mobilinkd/NucleoTNC/m17/images/m17-audio-output.png

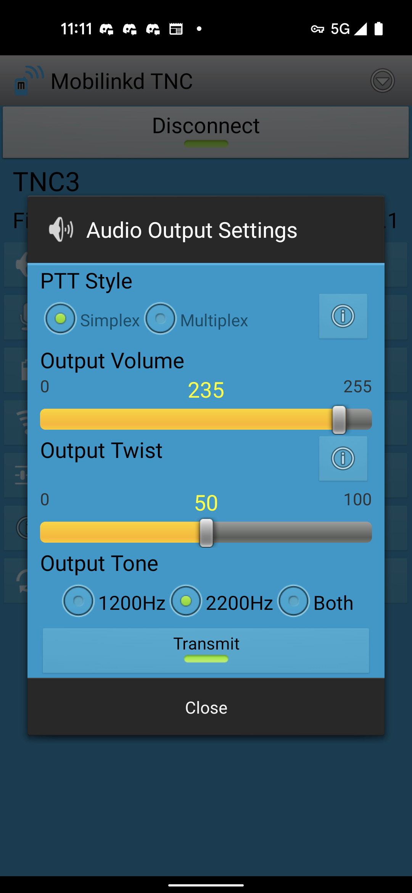
m17/images/m17-audio-output.png
