mobilinkd/NucleoTNC/m17/images/m17-bessel-null.png

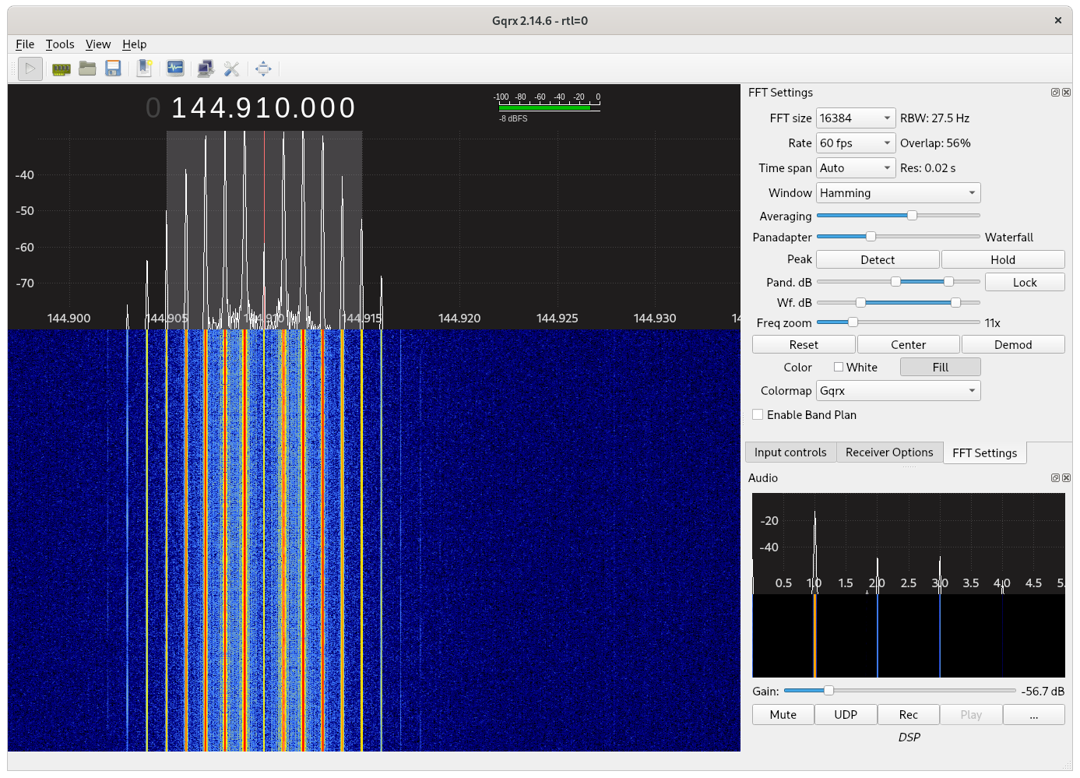
m17/images/m17-bessel-null.png
