mobilinkd/NucleoTNC/m17/images/m17-ht-voice-transmit.png

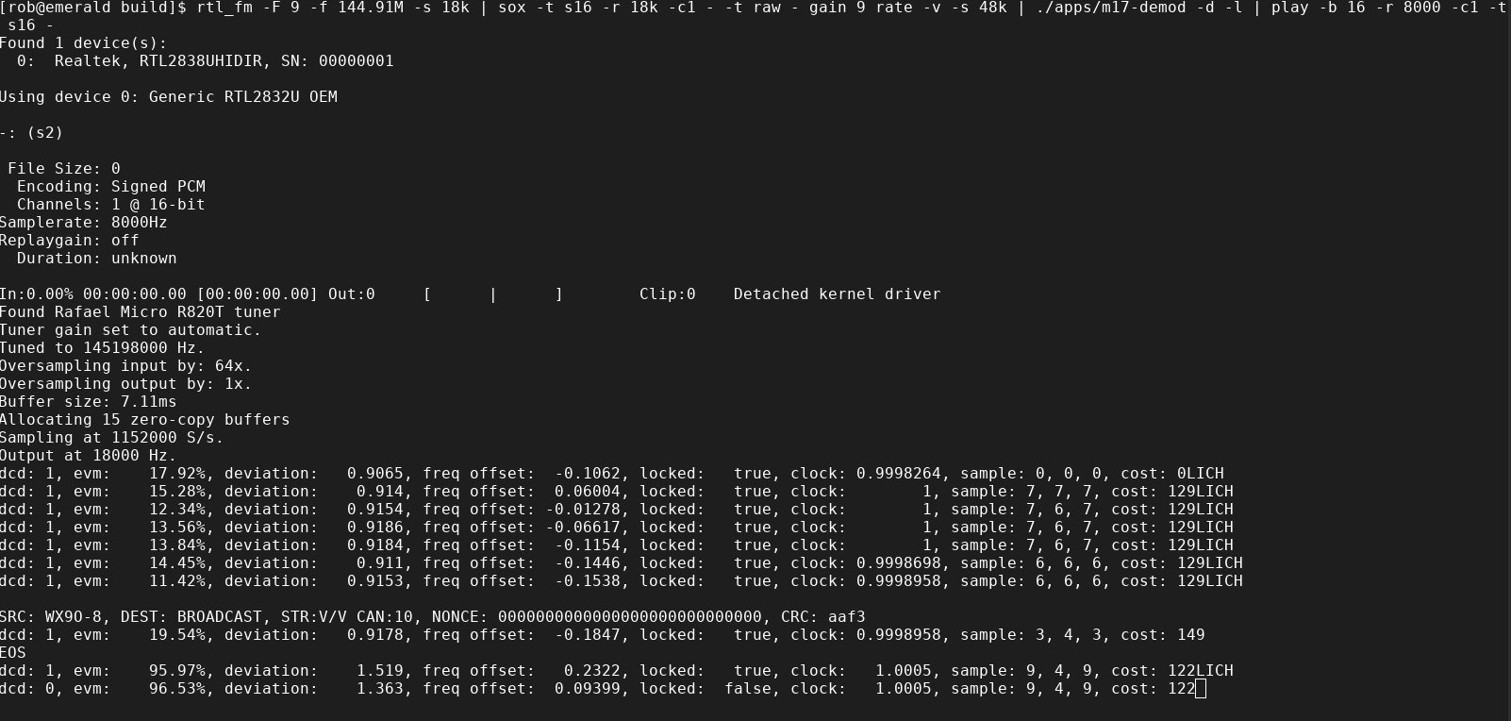
m17/images/m17-ht-voice-transmit.png
