mobilinkd/NucleoTNC/m17/images/m17-kiss-ht-callsign.png

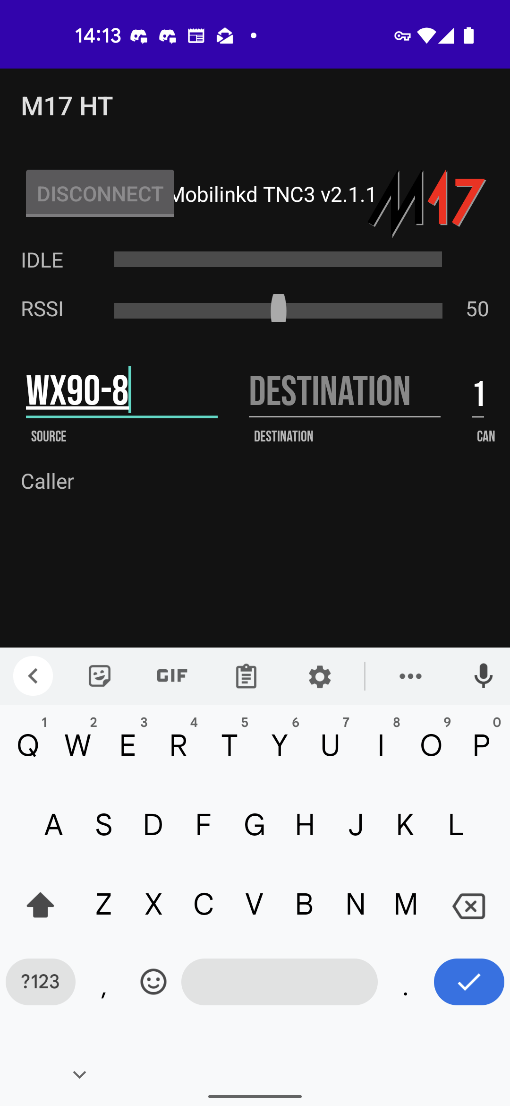
m17/images/m17-kiss-ht-callsign.png
