mobilinkd/NucleoTNC/m17/images/m17-modem-settings.png

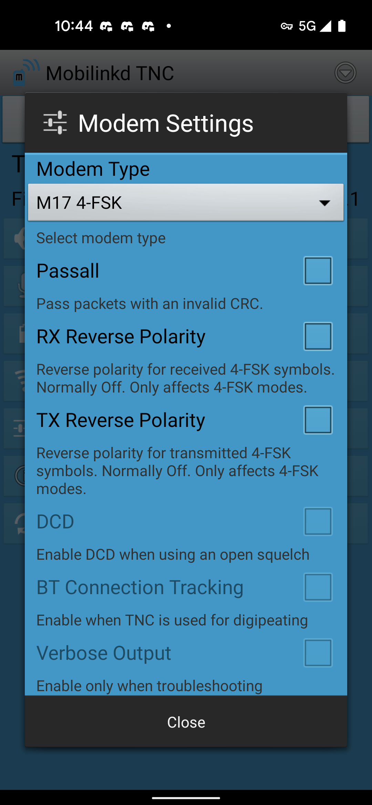
m17/images/m17-modem-settings.png
