mobilinkd/NucleoTNC/m17/images/m17-usb-connection.png

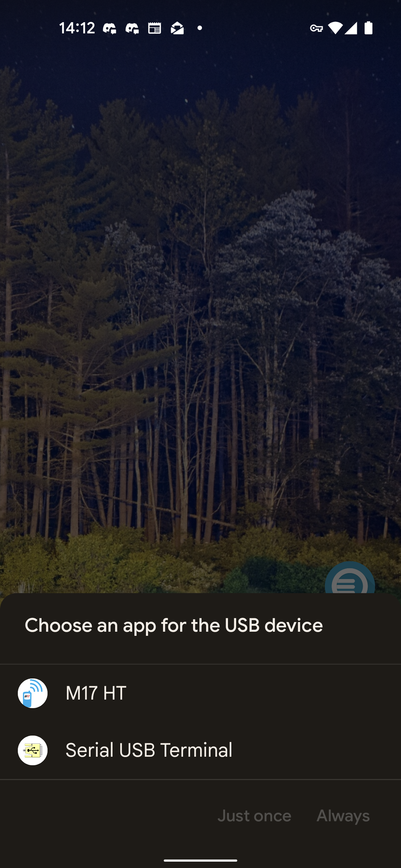
m17/images/m17-usb-connection.png
