mobilinkd/NucleoTNC/m17/images/wobbly-freq-accuracy.png

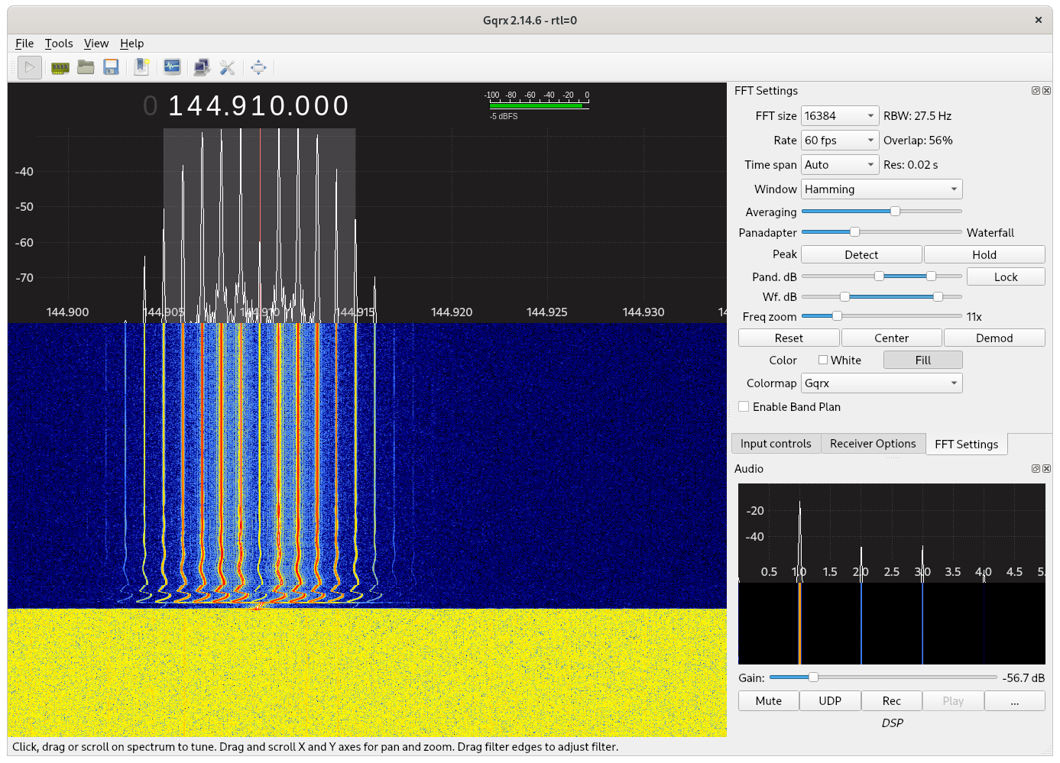
m17/images/wobbly-freq-accuracy.png
