mobilinkd/NucleoTNC/Build/AssemblyStep1.png

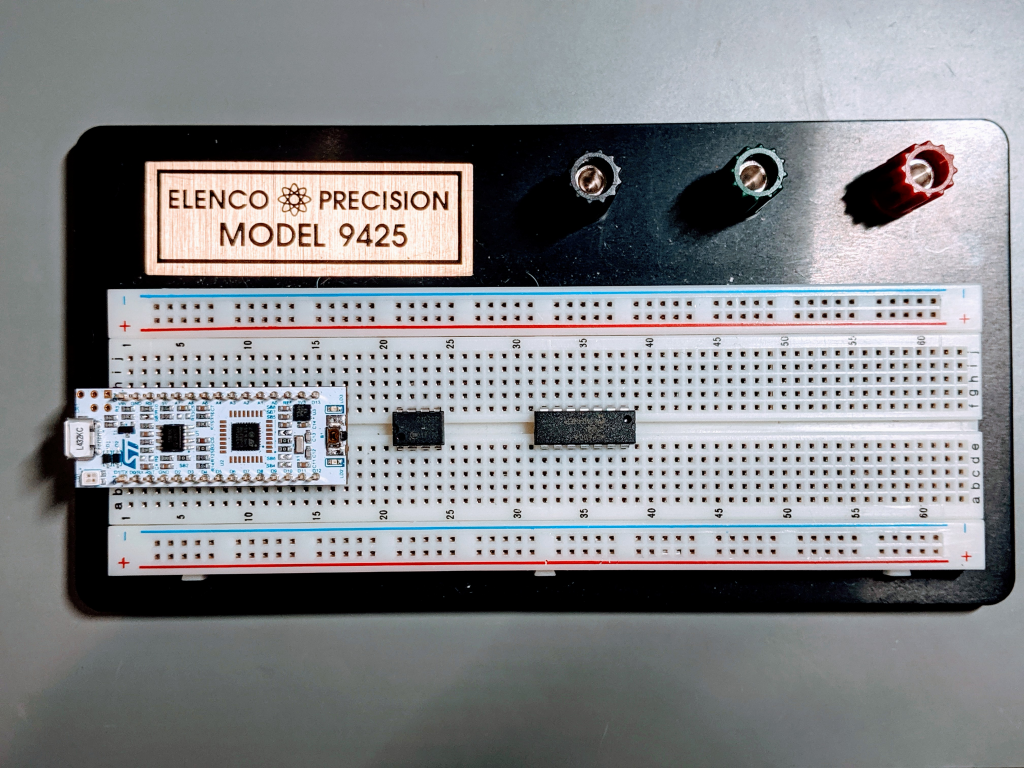
Build/AssemblyStep1.png
