mobilinkd/NucleoTNC/Build/AssemblyStep2.png

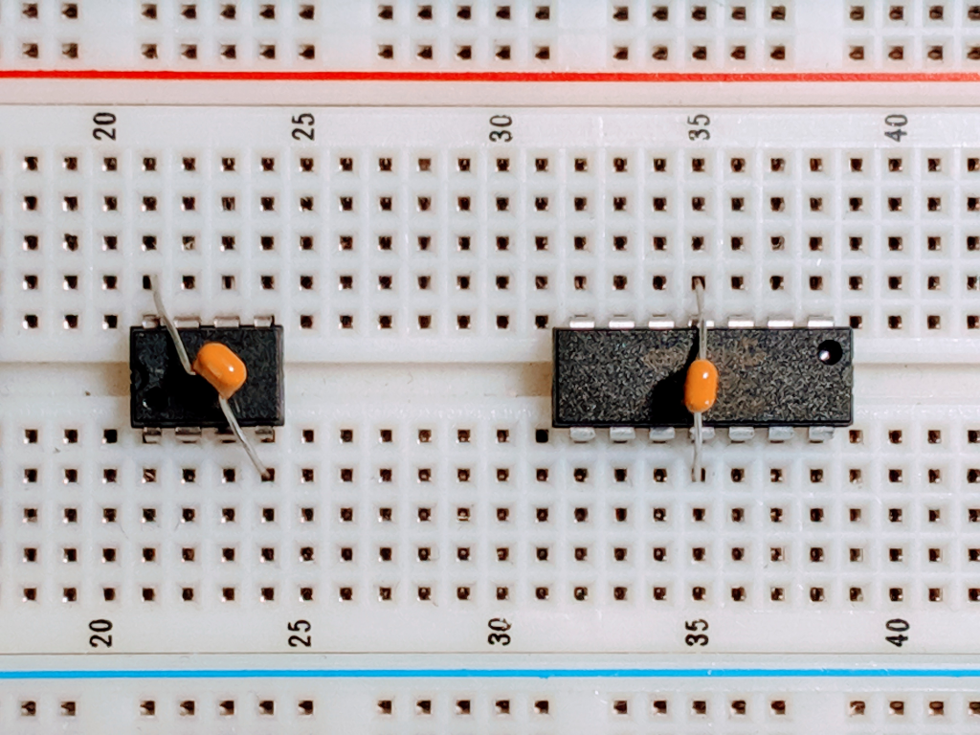
Build/AssemblyStep2.png
