mobilinkd/NucleoTNC/Build/AssemblyStep5.png

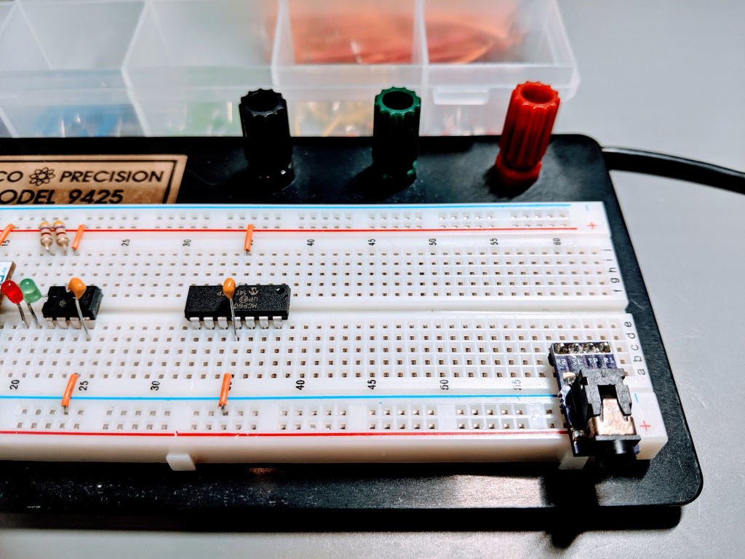
Build/AssemblyStep5.png
