mobilinkd/NucleoTNC/Build/AssemblyStep6.png

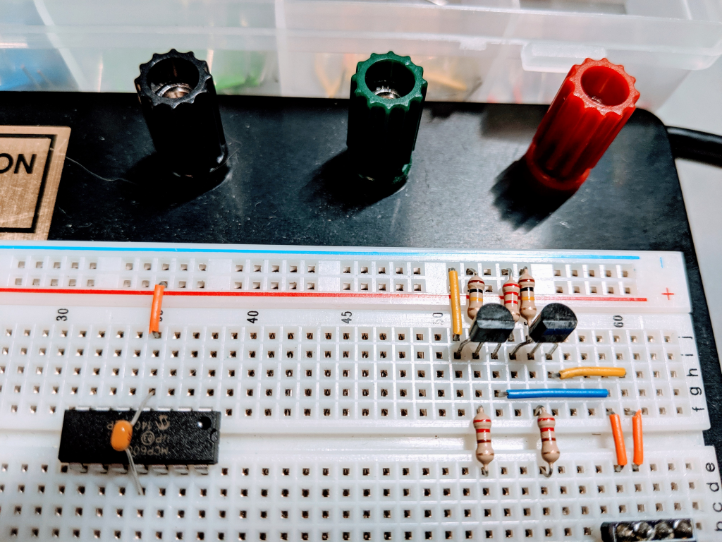
Build/AssemblyStep6.png
