mobilinkd/NucleoTNC/Build/AssemblyStep7.png

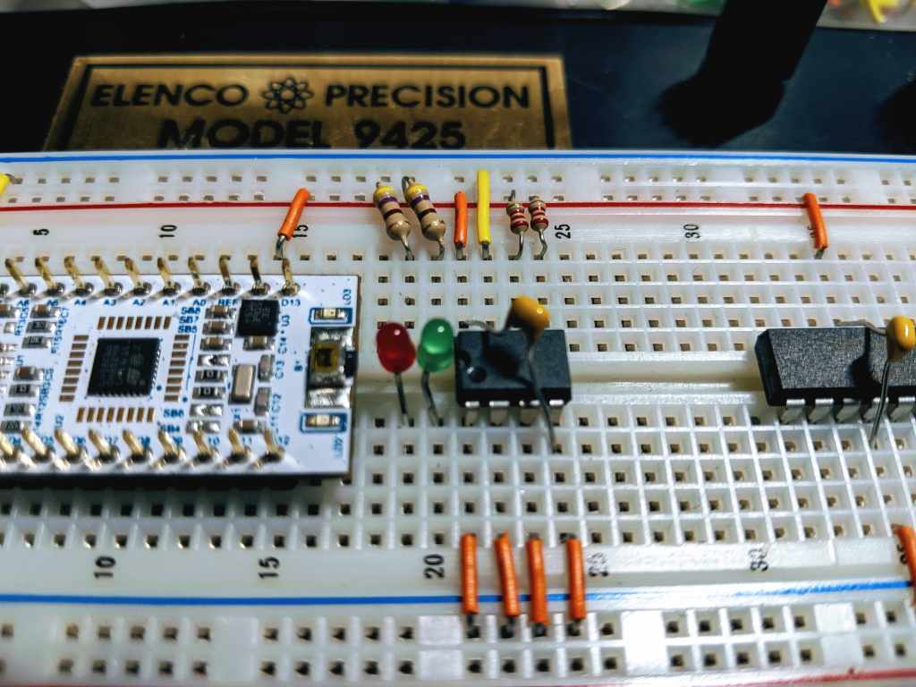
Build/AssemblyStep7.png
