mobilinkd/NucleoTNC/Build/AssemblyStep8.png

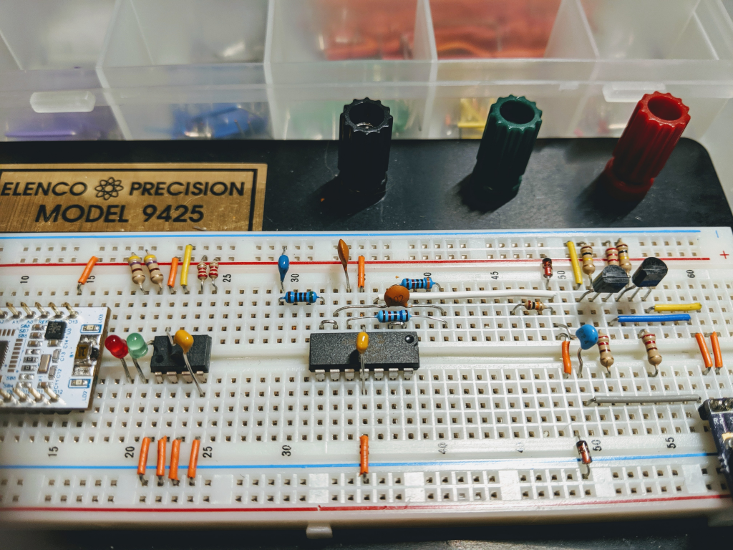
Build/AssemblyStep8.png
