mobilinkd/NucleoTNC/Build/AssemblyStep9.png

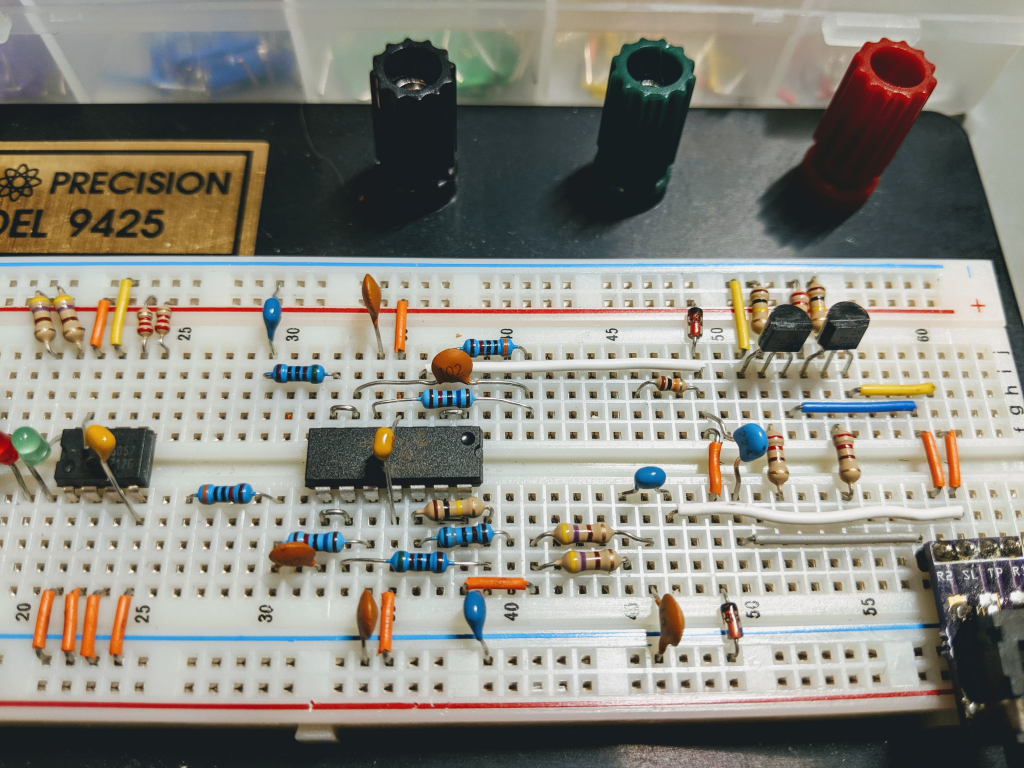
Build/AssemblyStep9.png
