mobilinkd/NucleoTNC/Build/TncConfigApp-Connect.png

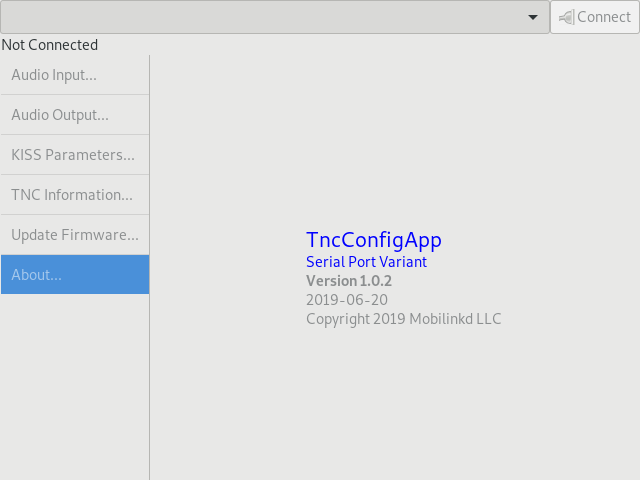
Build/TncConfigApp-Connect.png
