mobilinkd/NucleoTNC/Build/TncConfigApp-Info.png

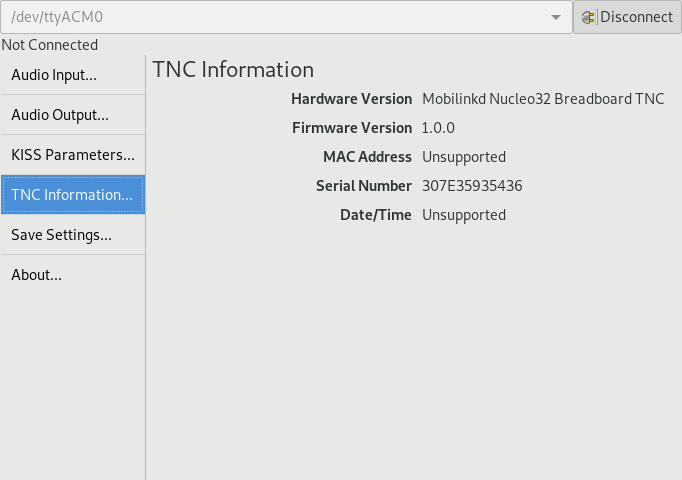
Build/TncConfigApp-Info.png
