mobilinkd/NucleoTNC/Build/TncConfigApp-Output.png

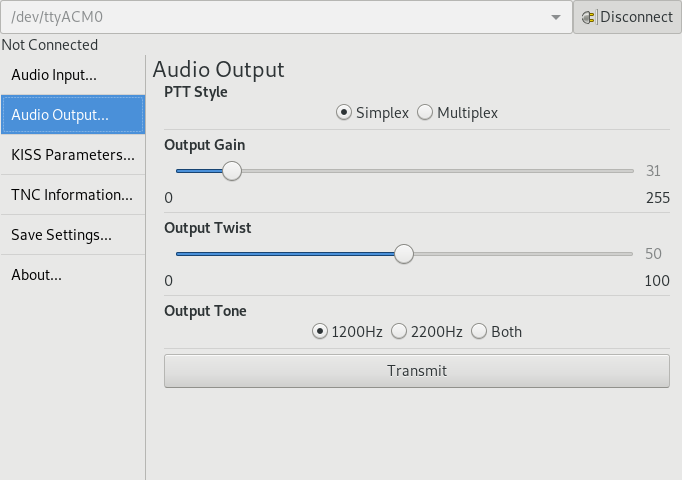
Build/TncConfigApp-Output.png
