mobilinkd/NucleoTNC/m17/images/m17-ber-test-1.png

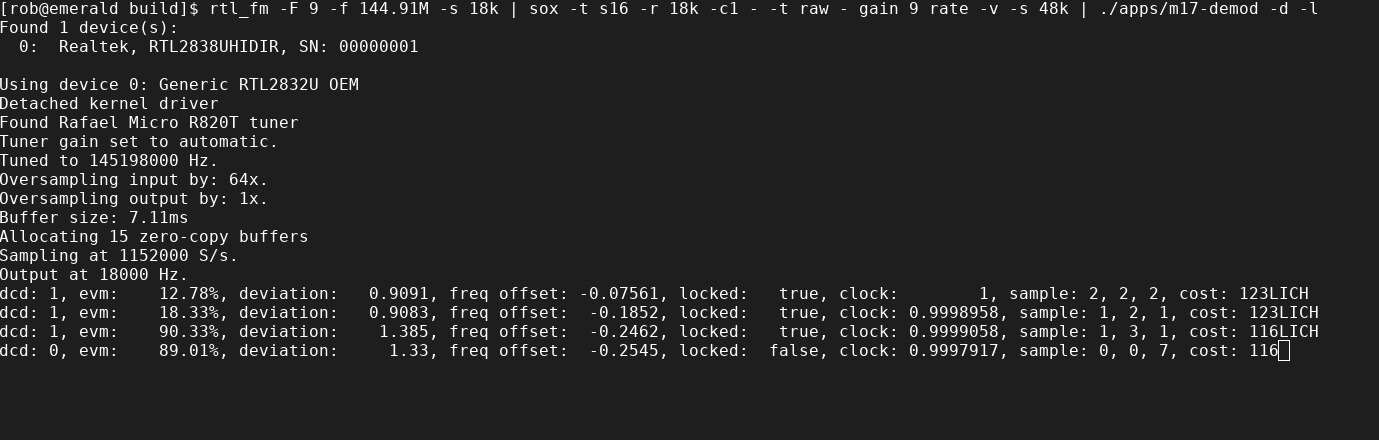
m17/images/m17-ber-test-1.png
