mobilinkd/NucleoTNC/m17/images/m17-ber-test-2.png

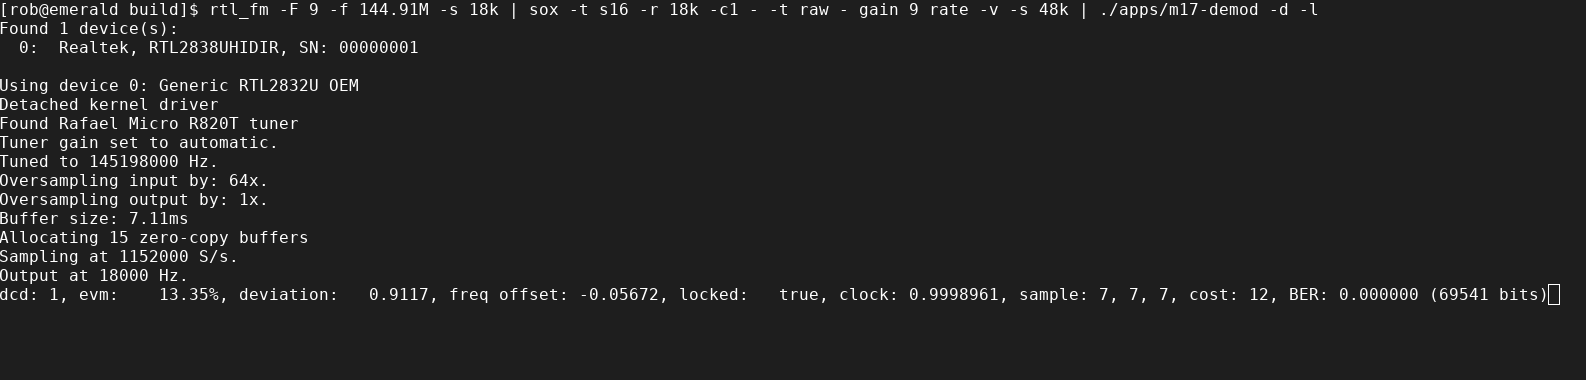
m17/images/m17-ber-test-2.png
