mobilinkd/NucleoTNC/m17/images/m17-rx-ber-test.png

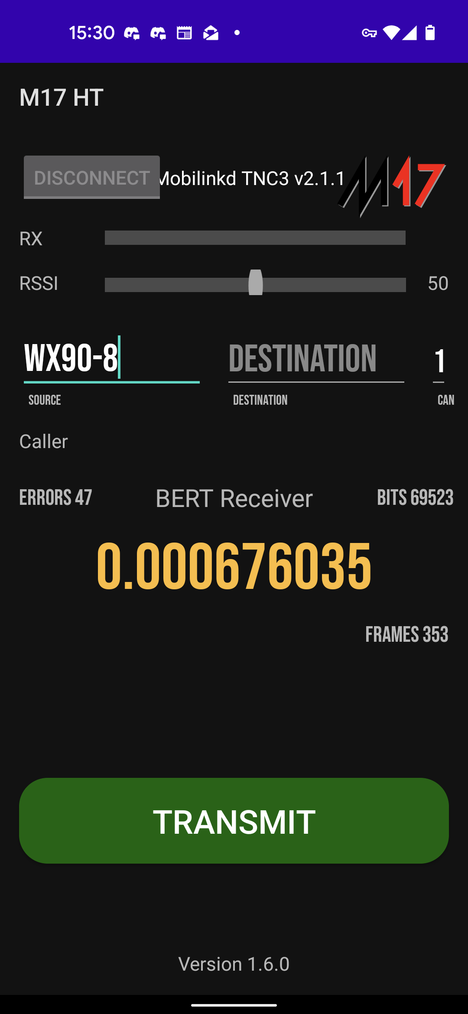
m17/images/m17-rx-ber-test.png
