mobilinkd/NucleoTNC/m17/images/m17-rx-voice-test.png

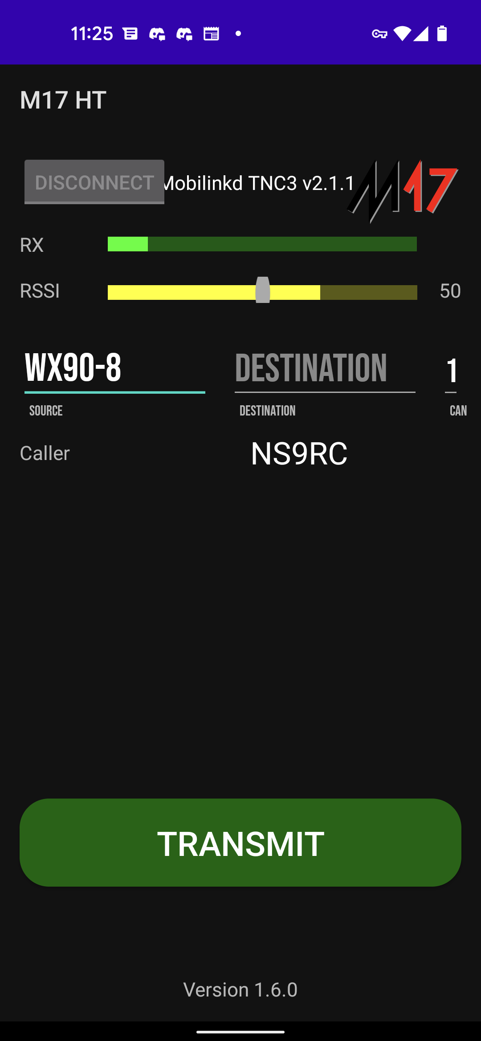
m17/images/m17-rx-voice-test.png
