mobilinkd/NucleoTNC/TNC/Fsk9600Demodulator.cpp

// Copyright 2020 Rob Riggs <rob@mobilinkd.com>
// All rights reserved.

#include "Fsk9600Demodulator.hpp"
#include "Goertzel.h"
#include "AudioInput.hpp"
#include "GPIO.hpp"
#include "Log.h"

namespace mobilinkd { namespace tnc {

hdlc::IoFrame* Fsk9600Demodulator::operator()(const q15_t* samples)
{
    hdlc::IoFrame* result = nullptr;

    auto filtered = demod_filter.filter(const_cast<q15_t* >(samples));

    for (size_t i = 0; i != ADC_BLOCK_SIZE; ++i)
    {
        auto sample = filtered[i];

        bool bit = sample >= 0;
        auto pll = pll_(bit);

        if (pll.sample)
        {
            locked_ = pll.locked;

            // We will only ever get one frame because there are
            // not enough bits in a block for more than one.
            if (result) {
                auto tmp = hdlc_decoder_(nrzi_.decode(lfsr_(bit)), locked_);
                if (tmp) hdlc::release(tmp);
            } else {
                result = hdlc_decoder_(nrzi_.decode(lfsr_(bit)), locked_);
#ifdef KISS_LOGGING
                if (result) {
                    INFO("samples = %ld, mean = %d, dev = %d",
                        snr_.samples, int(snr_.mean), int(snr_.stdev()));
                    INFO("SNR = %dmB", int(snr_.SNR() * 100.0f));
                    snr_.reset();
                }
#endif
            }

#ifdef KISS_LOGGING
            if (hdlc_decoder_.active())
            {
                if (!decoding_)
                {
                    snr_.reset();
                    decoding_ = true;
                }
                snr_.capture(float(abs(sample)));
            } else {
                decoding_ = false;
            }
#endif
        }

    }
    return result;
}

/*
 * Return twist as a the difference in dB between mark and space.  The
 * expected values are about 0dB for discriminator output and about 5.5dB
 * for de-emphasized audio.
 */
float Fsk9600Demodulator::readTwist()
{
    TNC_DEBUG("enter Fsk9600Demodulator::readTwist");

    float g120 = 0.0f;
    float g4800 = 0.0f;

    GoertzelFilter<ADC_BLOCK_SIZE, SAMPLE_RATE> gf120(120.0, 0);
    GoertzelFilter<ADC_BLOCK_SIZE, SAMPLE_RATE> gf4800(4800.0, 0);

    const uint32_t AVG_SAMPLES = 160;

    startADC(416, ADC_BLOCK_SIZE);

    for (uint32_t i = 0; i != AVG_SAMPLES; ++i)
    {
        uint32_t count = 0;
        while (count < ADC_BLOCK_SIZE)
        {
            osEvent evt = osMessageGet(adcInputQueueHandle, osWaitForever);
            if (evt.status != osEventMessage)
                continue;

            auto block = (audio::adc_pool_type::chunk_type*) evt.value.p;
            uint16_t* data = (uint16_t*) block->buffer;
            gf120(data, ADC_BLOCK_SIZE);
            gf4800(data, ADC_BLOCK_SIZE);

            audio::adcPool.deallocate(block);

            count += ADC_BLOCK_SIZE;
        }

        g120 += (gf120 / count);
        g4800 += (gf4800 / count);

        gf120.reset();
        gf4800.reset();
    }

    IDemodulator::stopADC();

    g120 = 10.0f * log10f(g120 / AVG_SAMPLES);
    g4800 = 10.0f * log10f(g4800 / AVG_SAMPLES);

    auto result = g120 - g4800;

    INFO("9600 Twist = %d / 100 (%d - %d)", int(result * 100), int(g120 * 100),
        int(g4800 * 100));

    TNC_DEBUG("exit Fsk9600Demodulator::readTwist");
    return result;
}

uint32_t Fsk9600Demodulator::readBatteryLevel()
{
#ifndef NUCLEOTNC
    TNC_DEBUG("enter Fsk9600Demodulator::readBatteryLevel");

    ADC_ChannelConfTypeDef sConfig;

    sConfig.Channel = ADC_CHANNEL_VREFINT;
    sConfig.Rank = ADC_REGULAR_RANK_1;
    sConfig.SingleDiff = ADC_SINGLE_ENDED;
    sConfig.SamplingTime = ADC_SAMPLETIME_247CYCLES_5;
    sConfig.OffsetNumber = ADC_OFFSET_NONE;
    sConfig.Offset = 0;
    if (HAL_ADC_ConfigChannel(&hadc1, &sConfig) != HAL_OK)
        CxxErrorHandler();

    htim6.Init.Period = 48000;
    if (HAL_TIM_Base_Init(&htim6) != HAL_OK) CxxErrorHandler();

    if (HAL_TIM_Base_Start(&htim6) != HAL_OK)
        CxxErrorHandler();

    if (HAL_ADC_Start(&hadc1) != HAL_OK) CxxErrorHandler();
    if (HAL_ADC_PollForConversion(&hadc1, 3) != HAL_OK) CxxErrorHandler();
    auto vrefint = HAL_ADC_GetValue(&hadc1);
    if (HAL_ADC_Stop(&hadc1) != HAL_OK) CxxErrorHandler();

    // Disable battery charging while measuring battery voltage.
    auto usb_ce = gpio::USB_CE::get();
    gpio::USB_CE::on();

    gpio::BAT_DIVIDER::off();
    HAL_Delay(1);

    sConfig.Channel = BATTERY_ADC_CHANNEL;
    if (HAL_ADC_ConfigChannel(&BATTERY_ADC_HANDLE, &sConfig) != HAL_OK)
        CxxErrorHandler();

    uint32_t vbat = 0;
    if (HAL_ADC_Start(&BATTERY_ADC_HANDLE) != HAL_OK) CxxErrorHandler();
    for (size_t i = 0; i != 8; ++i)
    {
        if (HAL_ADC_PollForConversion(&BATTERY_ADC_HANDLE, 1) != HAL_OK) CxxErrorHandler();
        vbat += HAL_ADC_GetValue(&BATTERY_ADC_HANDLE);
    }

    vbat /= 8;

    if (HAL_ADC_Stop(&BATTERY_ADC_HANDLE) != HAL_OK) CxxErrorHandler();
    if (HAL_TIM_Base_Stop(&htim6) != HAL_OK)
        CxxErrorHandler();

    gpio::BAT_DIVIDER::on();

    // Restore battery charging state.
    if (!usb_ce) gpio::USB_CE::off();

    INFO("Vref = %lu", vrefint);
    INFO("Vbat = %lu (raw)", vbat);

    // Order of operations is important to avoid underflow.
    vbat *= 6600;
    vbat /= (VREF + 1);

    uint32_t vref = ((vrefint * 3300) + (VREF / 2)) / VREF;

    INFO("Vref = %lumV", vref)
    INFO("Vbat = %lumV", vbat);

    TNC_DEBUG("exit Fsk9600Demodulator::readBatteryLevel");
    return vbat;
#else
    return 0;
#endif
}

const Fsk9600Demodulator::bpf_bank_type Fsk9600Demodulator::bpf_bank = {{
    // -3dB
    {{
            1,     0,     0,     0,     0,     0,    -1,    -1,    -1,    -1,     0,     0,
            0,     0,     1,     2,     2,     3,     2,     2,     0,     0,    -2,    -3,
           -4,    -4,    -3,    -1,     3,     9,    17,    27,    38,    48,    58,    65,
           68,    67,    60,    46,    25,    -1,   -32,   -67,  -102,  -135,  -160,  -175,
         -174,  -153,  -110,   -41,    54,   178,   327,   500,   692,   897,  1109,  1318,
         1518,  1700,  1857,  1981,  2067,  2110,  2110,  2067,  1981,  1857,  1700,  1518,
         1318,  1109,   897,   692,   500,   327,   178,    54,   -41,  -110,  -153,  -174,
         -175,  -160,  -135,  -102,   -67,   -32,    -1,    25,    46,    60,    67,    68,
           65,    58,    48,    38,    27,    17,     9,     3,    -1,    -3,    -4,    -4,
           -3,    -2,     0,     0,     2,     2,     3,     2,     2,     1,     0,     0,
            0,     0,    -1,    -1,    -1,    -1,     0,     0,     0,     0,     0,     1
    }},
    // -2dB
    {{
            1,     0,     0,     0,     0,    -1,    -1,    -1,    -1,    -1,    -1,    -1,
            0,     0,     1,     1,     2,     2,     1,     0,     0,    -1,    -3,    -5,
           -6,    -6,    -5,    -1,     3,    10,    20,    31,    42,    54,    64,    72,
           75,    72,    63,    46,    21,   -11,   -49,   -92,  -135,  -175,  -208,  -229,
         -233,  -216,  -173,  -102,     0,   131,   293,   481,   691,   915,  1147,  1378,
         1598,  1799,  1971,  2108,  2203,  2251,  2251,  2203,  2108,  1971,  1799,  1598,
         1378,  1147,   915,   691,   481,   293,   131,     0,  -102,  -173,  -216,  -233,
         -229,  -208,  -175,  -135,   -92,   -49,   -11,    21,    46,    63,    72,    75,
           72,    64,    54,    42,    31,    20,    10,     3,    -1,    -5,    -6,    -6,
           -5,    -3,    -1,     0,     0,     1,     2,     2,     1,     1,     0,     0,
           -1,    -1,    -1,    -1,    -1,    -1,    -1,     0,     0,     0,     0,     1
    }},
    // -1dB
    {{
            1,     0,     0,     0,     0,    -1,    -1,    -2,    -2,    -2,    -2,    -1,
           -1,     0,     0,     0,     1,     1,     0,     0,    -1,    -3,    -5,    -7,
           -8,    -8,    -6,    -2,     3,    11,    22,    34,    48,    60,    72,    80,
           82,    78,    66,    45,    15,   -22,   -68,  -119,  -171,  -221,  -262,  -291,
         -300,  -286,  -244,  -170,   -62,    79,   255,   460,   689,   936,  1191,  1445,
         1688,  1909,  2100,  2251,  2356,  2410,  2410,  2356,  2251,  2100,  1909,  1688,
         1445,  1191,   936,   689,   460,   255,    79,   -62,  -170,  -244,  -286,  -300,
         -291,  -262,  -221,  -171,  -119,   -68,   -22,    15,    45,    66,    78,    82,
           80,    72,    60,    48,    34,    22,    11,     3,    -2,    -6,    -8,    -8,
           -7,    -5,    -3,    -1,     0,     0,     1,     1,     0,     0,     0,    -1,
           -1,    -2,    -2,    -2,    -2,    -1,    -1,     0,     0,     0,     0,     1
    }},
    // 0dB
    {{
            1,     0,     0,     0,    -1,    -1,    -2,    -2,    -3,    -3,    -3,    -2,
           -2,    -1,     0,     0,     0,     0,     0,    -1,    -3,    -5,    -7,    -9,
          -10,   -10,    -7,    -3,     3,    13,    25,    39,    53,    68,    80,    88,
           91,    85,    70,    45,     9,   -35,   -90,  -150,  -212,  -272,  -323,  -359,
         -376,  -366,  -324,  -247,  -132,    21,   212,   436,   688,   959,  1240,  1520,
         1789,  2034,  2244,  2412,  2528,  2587,  2587,  2528,  2412,  2244,  2034,  1789,
         1520,  1240,   959,   688,   436,   212,    21,  -132,  -247,  -324,  -366,  -376,
         -359,  -323,  -272,  -212,  -150,   -90,   -35,     9,    45,    70,    85,    91,
           88,    80,    68,    53,    39,    25,    13,     3,    -3,    -7,   -10,   -10,
           -9,    -7,    -5,    -3,    -1,     0,     0,     0,     0,     0,    -1,    -2,
           -2,    -3,    -3,    -3,    -2,    -2,    -1,    -1,     0,     0,     0,     1
    }},
    // 1dB
    {{
            1,     1,     0,     0,    -1,    -2,    -2,    -3,    -3,    -4,    -4,    -3,
           -3,    -2,    -1,    -1,    -1,    -1,    -1,    -3,    -5,    -7,    -9,   -11,
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
          -44,   -40,   -35,   -30,   -25,   -21,   -18,   -17,   -16,   -16,   -16,   -17,
          -17,   -16,   -15,   -14,   -12,    -9,    -7,    -4,    -2,     0,     2,     3
    }}
}};

}} // mobilinkd::tnc
