mobilinkd/NucleoTNC/TNC/Goertzel.cpp

// Copyright 2017 Rob Riggs <rob@mobilinkd.com>
// All rights reserved.

#include "Goertzel.h"

namespace mobilinkd { namespace tnc {

#if 1
const float WINDOW[] = {
  0.006878,
  0.00687800535762,
  0.00687802143048,
  0.00687804821858,
  0.00687808572193,
  0.00687813394055,
  0.00687819287442,
  0.00687826252358,
  0.00687834288804,
  0.00687843396781,
  0.00687853576292,
  0.00687864827338,
  0.00687877149922,
  0.00687890544047,
  0.00687905009716,
  0.00687920546932,
  0.00687937155698,
  0.00687954836018,
  0.00687973587896,
  0.00687993411336,
  0.00688014306342,
  0.0068803627292,
  0.00688059311073,
  0.00688083420806,
  0.00688108602126,
  0.00688134855038,
  0.00688162179547,
  0.00688190575659,
  0.00688220043381,
  0.00688250582719,
  0.0068828219368,
  0.0068831487627,
  0.00688348630498,
  0.0068838345637,
  0.00688419353893,
  0.00688456323077,
  0.00688494363928,
  0.00688533476456,
  0.00688573660669,
  0.00688614916575,
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

};

#endif

}} // mobilinkd::tnc
