mobilinkd/NucleoTNC/TNC/FilterCoefficients.hpp

// Copyright 2015-2020 Rob Riggs <rob@mobilinkd.com>
// All rights reserved.

#pragma once

#include "IirFilter.hpp"
#include "FirFilter.hpp"

namespace mobilinkd { namespace tnc { namespace filter {

namespace fir {

// 1200Hz = -12dB, 2200Hz = 0dB; 3653Hz cutoff, 4.93 gain; cosine.
const TFirCoefficients<9> dB12 = {
    {
        0.0223997567081,
        -0.132588208904,
        -0.590869965255,
        -1.12325491747,
        3.55525416434,
        -1.12325491747,
        -0.590869965255,
        -0.132588208904,
        0.0223997567081,
    }
};

// 1200Hz = -11dB, 2200Hz = 0dB; 3537Hz cutoff, 4.51 gain; cosine.
const TFirCoefficients<9> dB11 = {
    {
        0.0138943225784,
        -0.137800909104,
        -0.544488104185,
        -1.00269495093,
        3.29019584315,
        -1.00269495093,
        -0.544488104185,
        -0.137800909104,
        0.0138943225784,
    }
};

// 1200Hz = -10dB, 2200Hz = 0dB; 3405Hz cutoff, 4.11 gain; cosine.
const TFirCoefficients<9> dB10 = {
    {
        0.00564557245371,
        -0.141643920093,
        -0.498513944796,
        -0.887264289827,
        3.03792032485,
        -0.887264289827,
        -0.498513944796,
        -0.141643920093,
        0.00564557245371,
    }
};

// 1200Hz = -9dB, 2200Hz = 0dB; 3252Hz cutoff, 3.7 gain; cosine.
const TFirCoefficients<9> dB9 = {
    {
        -0.00232554104135,
        -0.142858725752,
        -0.449053780255,
        -0.770264863826,
        2.77651146344,
        -0.770264863826,
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
const TFirCoefficients<9> dB_4 = {
    {
        0.0498539382844,
        0.103801174967,
        0.153695746099,
        0.188874162863,
        0.201549955573,
        0.188874162863,
        0.153695746099,
        0.103801174967,
        0.0498539382844,
    }
};

// 1200Hz = 0dB, 2200Hz = -5dB; 2174Hz cutoff, 1.237 gain; boxcar.
const TFirCoefficients<9> dB_5 = {
    {
        0.0782137588209,
        0.118736939542,
        0.153156300897,
        0.176223458893,
        0.184339083696,
        0.176223458893,
        0.153156300897,
        0.118736939542,
        0.0782137588209,
    }
};

// 1200Hz = 0dB, 2200Hz = -6dB; 1706Hz cutoff, 1.275 gain; boxcar.
const TFirCoefficients<9> dB_6 = {
    {
        0.104477241089,
        0.130913242609,
        0.151854419973,
        0.165293215366,
        0.169923761926,
        0.165293215366,
        0.151854419973,
        0.130913242609,
        0.104477241089,
    }
};

extern const TFirCoefficients<9>* AfskFilters[19];

} // fir


}}} // mobilinkd::tnc::filter
