mobilinkd/NucleoTNC/TNC/AFSKTestTone.hpp

// Copyright 2016-2021 Rob Riggs <rob@mobilinkd.com>
// All rights reserved.

#pragma once

#include "cmsis_os.h"

extern "C" void startAfskToneTask(void* arg);

namespace mobilinkd { namespace tnc {

struct AFSKTestTone
{
    enum class State {MARK, SPACE, BOTH, NONE};
    AFSKTestTone();
    void transmit(State prev);
    void mark();
    void space();
    void both();
    void stop();
    void fill() const;
    State state() const { return state_; }

    State state_{State::NONE};
    osThreadId testToneTask_{0};
};

}} // mobilinkd::tnc
