mobilinkd/NucleoTNC/TNC/FirFilter.cpp

// Copyright 2015-2021 Rob Riggs <rob@mobilinkd.com>
// All rights reserved.

#include "FirFilter.hpp"

namespace mobilinkd { namespace tnc { namespace fir_detail {

//float filter_input[MAX_BLOCK_SIZE];
//float filter_output[MAX_BLOCK_SIZE];

}}} // mobilinkd::tnc::fir_detail
